R4ph3rd/totem_panic/indian_music/notes.h

  #define NOTE_DO1   33
#define NOTE_DOD1  35
#define NOTE_RE1   37
#define NOTE_RED1  39
#define NOTE_MI1   41
#define NOTE_FA1   44
#define NOTE_FAD1  46
#define NOTE_SOL1  49
#define NOTE_SOLD1 52
#define NOTE_LA1   55
#define NOTE_LAD1  58
#define NOTE_SI1   62
#define NOTE_DO2   65
#define NOTE_DOD2  69
#define NOTE_RE2   73
#define NOTE_RED2  78
#define NOTE_MI2   82
#define NOTE_FA2   87
#define NOTE_FAD2  93
#define NOTE_SOL2  98
#define NOTE_SOLD2 104
#define NOTE_LA2   110
#define NOTE_LAD2  117
#define NOTE_SI2   123
#define NOTE_DO3   131
#define NOTE_DOD3  139
#define NOTE_RE3   147
#define NOTE_RED3  156
#define NOTE_MI3   165
#define NOTE_FA3   175
#define NOTE_FAD3  185
#define NOTE_SOL3  196
#define NOTE_SOLD3 208
#define NOTE_LA3   220
#define NOTE_LAD3  233
#define NOTE_SI3   247
#define NOTE_DO4   262
#define NOTE_DOD4  277
#define NOTE_RE4   294
#define NOTE_RED4  311
#define NOTE_MI4   330
#define NOTE_FA4   349
#define NOTE_FAD4  370
#define NOTE_SOL4  392
#define NOTE_SOLD4 415
#define NOTE_LA4   440
#define NOTE_LAD4  466
#define NOTE_SI4   494
#define NOTE_DO5   523
#define NOTE_DOD5  554
#define NOTE_RE5   587
#define NOTE_RED5  622
#define NOTE_MI5   659
#define NOTE_FA5   698
#define NOTE_FAD5  740
#define NOTE_SOL5  784
#define NOTE_SOLD5 831
#define NOTE_LA5   880
#define NOTE_LAD5  932
#define NOTE_SI5   988
#define NOTE_DO6   1047
#define NOTE_DOD6  1109
#define NOTE_RE6   1175
#define NOTE_RED6  1245
#define NOTE_MI6   1319
#define NOTE_FA6   1397
#define NOTE_FAD6  1480
#define NOTE_SOL6  1568
#define NOTE_SOLD6 1661
#define NOTE_LA6   1760
#define NOTE_LAD6  1865
#define NOTE_SI6   1976
#define NOTE_DO7   2093
#define NOTE_DOD7  2217
#define NOTE_RE7   2349
#define NOTE_RED7  2489
#define NOTE_MI7   2637
#define NOTE_FA7   2794
#define NOTE_FAD7  2960
#define NOTE_SOL7  3136
#define NOTE_SOLD7 3322
#define NOTE_LA7   3520
#define NOTE_LAD7  3729
#define NOTE_SI7   3951
#define NOTE_DO8   4186
#define NOTE_DOD8  4435
#define NOTE_RE8   4699
#define NOTE_RED8  4978
