R4ph3rd/totem_panic/totem_panic/notes.h

  #define  DO1   33
#define  DOD1  35
#define  RE1   37
#define  RED1  39
#define  MI1   41
#define  FA1   44
#define  FAD1  46
#define  SOL1  49
#define  SOLD1 52
#define  LA1   55
#define  LAD1  58
#define  SI1   62
#define  DO2   65
#define  DOD2  69
#define  RE2   73
#define  RED2  78
#define  MI2   82
#define  FA2   87
#define  FAD2  93
#define  SOL2  98
#define  SOLD2 104
#define  LA2   110
#define  LAD2  117
#define  SI2   123
#define  DO3   131
#define  DOD3  139
#define  RE3   147
#define  RED3  156
#define  MI3   165
#define  FA3   175
#define  FAD3  185
#define  SOL3  196
#define  SOLD3 208
#define  LA3   220
#define  LAD3  233
#define  SI3   247
#define  DO4   262
#define  DOD4  277
#define  RE4   294
#define  RED4  311
#define  MI4   330
#define  FA4   349
#define  FAD4  370
#define  SOL4  392
#define  SOLD4 415
#define  LA4   440
#define  LAD4  466
#define  SI4   494
#define  DO5   523
#define  DOD5  554
#define  RE5   587
#define  RED5  622
#define  MI5   659
#define  FA5   698
#define  FAD5  740
#define  SOL5  784
#define  SOLD5 831
#define  LA5   880
#define  LAD5  932
#define  SI5   988
#define  DO6   1047
#define  DOD6  1109
#define  RE6   1175
#define  RED6  1245
#define  MI6   1319
#define  FA6   1397
#define  FAD6  1480
#define  SOL6  1568
#define  SOLD6 1661
#define  LA6   1760
#define  LAD6  1865
#define  SI6   1976
#define  DO7   2093
#define  DOD7  2217
#define  RE7   2349
#define  RED7  2489
#define  MI7   2637
#define  FA7   2794
#define  FAD7  2960
#define  SOL7  3136
#define  SOLD7 3322
#define  LA7   3520
#define  LAD7  3729
#define  SI7   3951
#define  DO8   4186
#define  DOD8  4435
#define  RE8   4699
#define  RED8  4978
